AdamSeidman/Basketball-Shot-Trainer/CAD/Adafruit BNO055/bottom.jpg

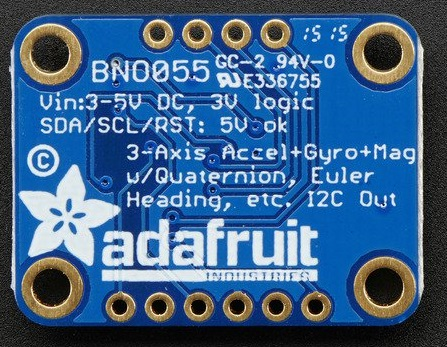
CAD/Adafruit BNO055/bottom.jpg
