AdamSeidman/Basketball-Shot-Trainer/CAD/Adafruit BNO055/Renderings/Render.png

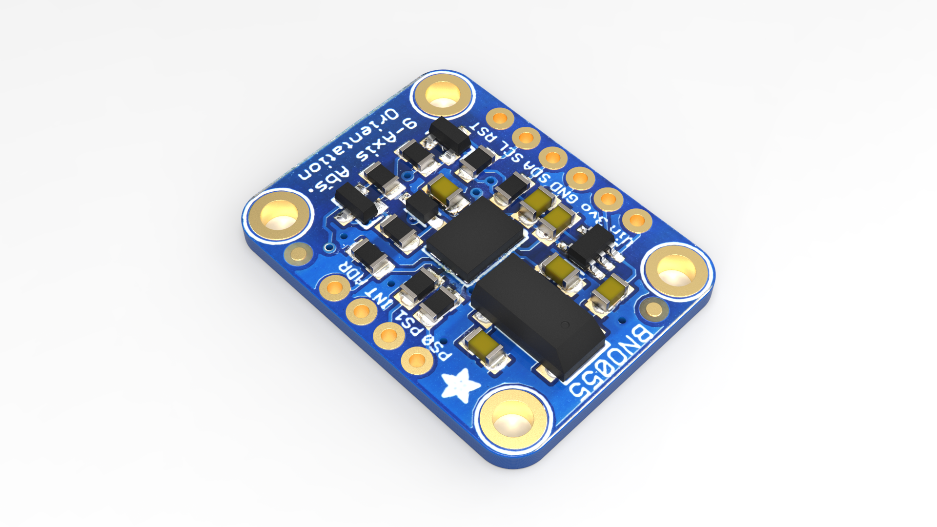
CAD/Adafruit BNO055/Renderings/Render.png
