AdamSeidman/Basketball-Shot-Trainer/CAD/Adafruit BNO055/top.jpg

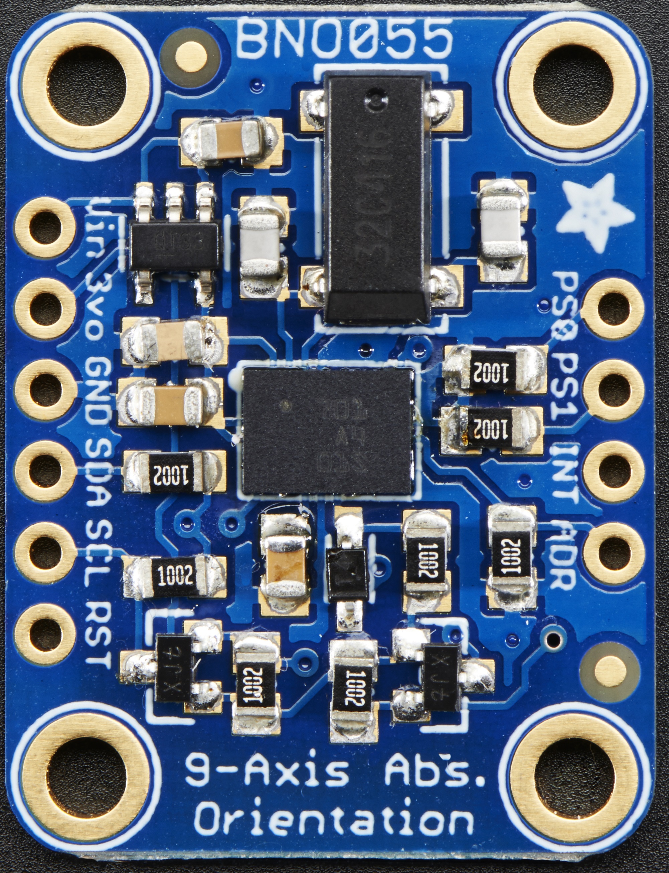
CAD/Adafruit BNO055/top.jpg
