AdamSeidman/Basketball-Shot-Trainer/Code/Python_Code/image1.png

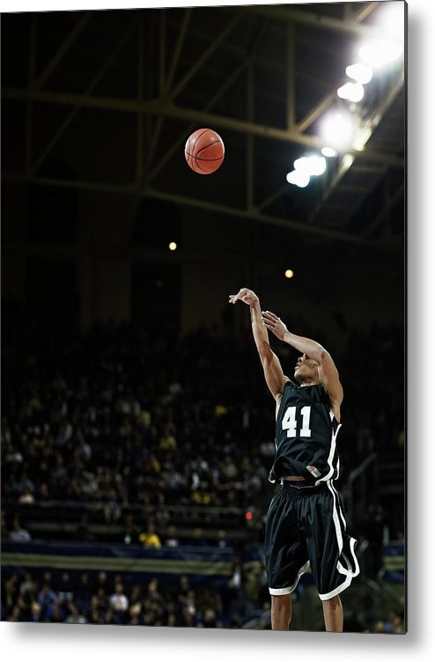
Code/Python_Code/image1.png
