AdamSeidman/Basketball-Shot-Trainer/Code/Python_Code/image3.jpg

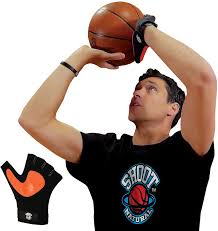
Code/Python_Code/image3.jpg
