AdamSeidman/Basketball-Shot-Trainer/Code/Python_Code/image4.jpg

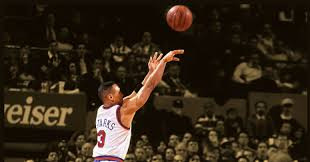
Code/Python_Code/image4.jpg
