AdamSeidman/Basketball-Shot-Trainer/Code/Python_Code/image28.png

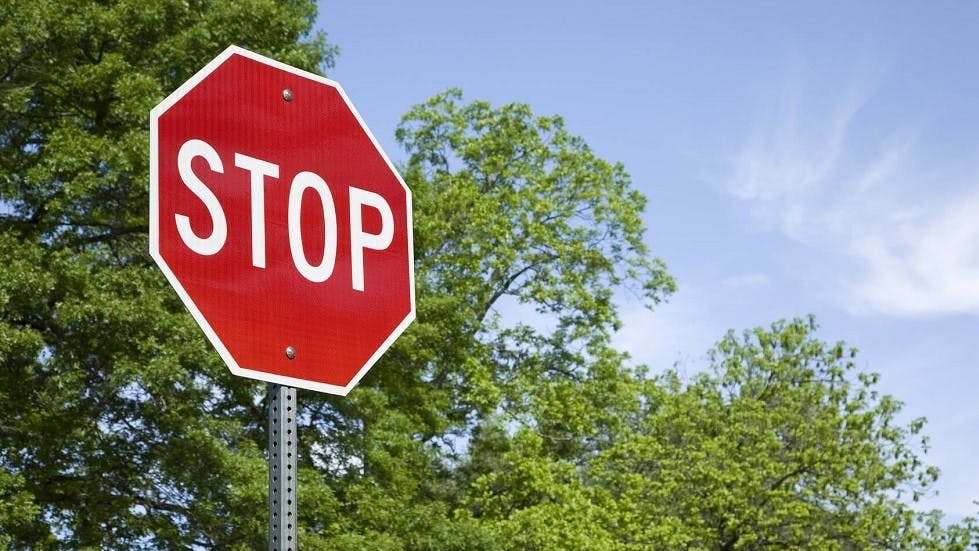
Code/Python_Code/image28.png
